croky-b/Boat_Engine_system_MAXI/Sound.ino

//
// =======================================================================================================
// SOUND
// =======================================================================================================
//




void triggerSound()
{
  if (Init)
  {
    
  Long_blast.Volume = LONG_VOL ;
  Short_blast.Volume = SHORT_VOL ;
  Bell.Volume = BELL_VOL ;
  Ancre.Volume = ANCOR_VOL ;
  Ambient.Volume = AMBIENT_VOL ;
  Seagull.Volume = SEAGULL_VOL ;
  Gun.Volume = GUN_VOL ;
  AAGun.Volume = AAGUN_VOL;
  Ring.Volume = ALARM2_VOL;
  Alarm.Volume = ALARM1_VOL;
  eleven1.Volume = ELEVEN1_VOL;
  eleven2.Volume = ELEVEN2_VOL;
  eleven3.Volume = ELEVEN3_VOL;
  eleven4.Volume = ELEVEN4_VOL;
  eleven5.Volume = ELEVEN5_VOL;
  eleven6.Volume = ELEVEN6_VOL;
  eleven7.Volume = ELEVEN7_VOL;
  eleven8.Volume = ELEVEN8_VOL;
  twelve1.Volume = TWELVE1_VOL;
  twelve2.Volume = TWELVE2_VOL;
  twelve3.Volume = TWELVE3_VOL;
  
    //
    // =======================================================================================================
    // STANDARD SOUND
    // =======================================================================================================
    //

    if (Seq6SoundPart1OnOff) {

#ifdef SEQ6_PART1_GUN

      if (Gun.Playing == false) {

        DacAudio.Play(&Gun, true);
      }
       if (Gun.TimeElapsed > 50 && Gun.TimeElapsed < 100 ) {
      cannonFlash = true;
    }

    else cannonFlash = false;
#endif

#ifdef SEQ6_PART1_AAGUN

      if (AAGun.Playing == false) {

        DacAudio.Play(&AAGun, true);
      }

       if (AAGun.TimeElapsed > 50 && AAGun.TimeElapsed < 80 ) {
      machinGunFlash = true;
    }

    else machinGunFlash = false;
#endif

#ifdef SEQ6_PART1_BELL

      if (Bell.Playing == false) {

        DacAudio.Play(&Bell, true);
      }
#endif

#ifdef SEQ6_PART1_SHORT

      if (Short_blast.Playing == false) {

        DacAudio.Play(&Short_blast, true);
      }
#endif

#ifdef SEQ6_PART1_LONG

      if (Long_blast.Playing == false) {

        DacAudio.Play(&Long_blast, true);
      }
#endif

#ifdef SEQ6_PART1_ALARM

      if (Alarm.Playing == false) {

        DacAudio.Play(&Alarm, true);
      }
#endif

#ifdef SEQ6_PART1_TWELVE1

      if (twelve1.Playing == false) {

        DacAudio.Play(&twelve1, true);
      }
#endif

#ifdef SEQ6_PART1_TWELVE2

      if (twelve2.Playing == false) {

        DacAudio.Play(&twelve2, true);
      }
#endif

#ifdef SEQ6_PART1_TWELVE3

      if (twelve3.Playing == false) {

        DacAudio.Play(&twelve3, true);
      }
#endif
    }


 if (Seq6SoundPart2OnOff) {

#ifdef SEQ6_PART2_GUN

      if (Gun.Playing == false) {

        DacAudio.Play(&Gun, true);
      }
       if (Gun.TimeElapsed > 50 && Gun.TimeElapsed < 100 ) {
      cannonFlash = true;
    }

    else cannonFlash = false;
#endif

#ifdef SEQ6_PART2_AAGUN

      if (AAGun.Playing == false) {

        DacAudio.Play(&AAGun, true);
      }

     if (AAGun.TimeElapsed > 50 && AAGun.TimeElapsed < 80 ) {
      machinGunFlash = true;
    }

    else machinGunFlash = false;
      
#endif

#ifdef SEQ6_PART2_BELL

      if (Bell.Playing == false) {

        DacAudio.Play(&Bell, true);
      }
#endif

#ifdef SEQ6_PART2_SHORT

      if (Short_blast.Playing == false) {

        DacAudio.Play(&Short_blast, true);
      }
#endif

#ifdef SEQ6_PART2_LONG

      if (Long_blast.Playing == false) {

        DacAudio.Play(&Long_blast, true);
      }
#endif

#ifdef SEQ6_PART2_ALARM

      if (Alarm.Playing == false) {

        DacAudio.Play(&Alarm, true);
      }
#endif

#ifdef SEQ6_PART2_TWELVE1

      if (twelve1.Playing == false) {

        DacAudio.Play(&twelve1, true);
      }
#endif

#ifdef SEQ6_PART2_TWELVE2

      if (twelve2.Playing == false) {

        DacAudio.Play(&twelve2, true);
      }
#endif

#ifdef SEQ6_PART2_TWELVE3

      if (twelve3.Playing == false) {

        DacAudio.Play(&twelve3, true);
      }
#endif
    }

 if (Seq6SoundPart3OnOff) {

#ifdef SEQ6_PART3_GUN

      if (Gun.Playing == false) {

        DacAudio.Play(&Gun, true);
      }

    if (Gun.TimeElapsed > 50 && Gun.TimeElapsed < 100 ) {
      cannonFlash = true;
    }

    else cannonFlash = false;
#endif

#ifdef SEQ6_PART3_AAGUN

      if (AAGun.Playing == false) {

        DacAudio.Play(&AAGun, true);
      }
 if (AAGun.TimeElapsed > 50 && AAGun.TimeElapsed < 80 ) {
      machinGunFlash = true;
    }

    else machinGunFlash = false;
#endif

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

      if (Long_blast.Playing == false) {

        DacAudio.Play(&Long_blast, true);
      }
#endif

#ifdef SEQ2_PART3_ALARM

      if (Alarm.Playing == false) {

        DacAudio.Play(&Alarm, true);
      }
#endif

#ifdef SEQ2_PART3_TWELVE1

      if (twelve1.Playing == false) {

        DacAudio.Play(&twelve1, true);
      }
#endif

#ifdef SEQ2_PART3_TWELVE2

      if (twelve2.Playing == false) {

        DacAudio.Play(&twelve2, true);
      }
#endif

#ifdef SEQ2_PART3_TWELVE3

      if (twelve3.Playing == false) {

        DacAudio.Play(&twelve3, true);
      }
#endif
    }

 if (Seq2SoundPart4OnOff) {

#ifdef SEQ2_PART4_GUN

      if (Gun.Playing == false) {

        DacAudio.Play(&Gun, true);
      }

       if (Gun.TimeElapsed > 50 && Gun.TimeElapsed < 100 ) {
      cannonFlash = true;
    }

    else cannonFlash = false;
#endif

#ifdef SEQ2_PART4_AAGUN

      if (AAGun.Playing == false) {

        DacAudio.Play(&AAGun, true);
      }

       if (AAGun.TimeElapsed > 50 && AAGun.TimeElapsed < 80 ) {
      machinGunFlash = true;
    }

    else machinGunFlash = false;
#endif

#ifdef SEQ2_PART4_BELL

      if (Bell.Playing == false) {

        DacAudio.Play(&Bell, true);
      }
#endif

#ifdef SEQ2_PART4_SHORT

      if (Short_blast.Playing == false) {

        DacAudio.Play(&Short_blast, true);
      }
#endif

#ifdef SEQ2_PART4_LONG

      if (Long_blast.Playing == false) {

        DacAudio.Play(&Long_blast, true);
      }
#endif

#ifdef SEQ2_PART4_ALARM

      if (Alarm.Playing == false) {

        DacAudio.Play(&Alarm, true);
      }
#endif

#ifdef SEQ2_PART4_TWELVE1

      if (twelve1.Playing == false) {

        DacAudio.Play(&twelve1, true);
      }
#endif

#ifdef SEQ2_PART4_TWELVE2

      if (twelve2.Playing == false) {

        DacAudio.Play(&twelve2, true);
      }
#endif

#ifdef SEQ2_PART4_TWELVE3

      if (twelve3.Playing == false) {

        DacAudio.Play(&twelve3, true);
      }
#endif
    }
    if (Seq60SoundPart1OnOff) {

#ifdef SEQ6B_PART1_GUN

      if (Gun.Playing == false) {

        DacAudio.Play(&Gun, true);
      }
       if (Gun.TimeElapsed > 50 && Gun.TimeElapsed < 100 ) {
      cannonFlash = true;
    }

    else cannonFlash = false;
#endif

#ifdef SEQ6B_PART1_AAGUN

      if (AAGun.Playing == false) {

        DacAudio.Play(&AAGun, true);
      }

       if (AAGun.TimeElapsed > 50 && AAGun.TimeElapsed < 80 ) {
      machinGunFlash = true;
    }

    else machinGunFlash = false;
#endif

#ifdef SEQ6B_PART1_BELL

      if (Bell.Playing == false) {

        DacAudio.Play(&Bell, true);
      }
#endif

#ifdef SEQ6B_PART1_SHORT

      if (Short_blast.Playing == false) {

        DacAudio.Play(&Short_blast, true);
      }
#endif

#ifdef SEQ6B_PART1_LONG

      if (Long_blast.Playing == false) {

        DacAudio.Play(&Long_blast, true);
      }
#endif

#ifdef SEQ6B_PART1_ALARM

      if (Alarm.Playing == false) {

        DacAudio.Play(&Alarm, true);
      }
#endif

#ifdef SEQ6B_PART1_TWELVE1

      if (twelve1.Playing == false) {

        DacAudio.Play(&twelve1, true);
      }
#endif

#ifdef SEQ6B_PART1_TWELVE2

      if (twelve2.Playing == false) {

        DacAudio.Play(&twelve2, true);
      }
#endif

#ifdef SEQ6B_PART1_TWELVE3

      if (twelve3.Playing == false) {

        DacAudio.Play(&twelve3, true);
      }
#endif
    }


 if (Seq60SoundPart2OnOff) {

#ifdef SEQ6B_PART2_GUN

      if (Gun.Playing == false) {

        DacAudio.Play(&Gun, true);
      }
       if (Gun.TimeElapsed > 50 && Gun.TimeElapsed < 100 ) {
      cannonFlash = true;
    }

    else cannonFlash = false;
#endif

#ifdef SEQ6B_PART2_AAGUN

      if (AAGun.Playing == false) {

        DacAudio.Play(&AAGun, true);
      }

     if (AAGun.TimeElapsed > 50 && AAGun.TimeElapsed < 80 ) {
      machinGunFlash = true;
    }

    else machinGunFlash = false;
      
#endif

#ifdef SEQ6B_PART2_BELL

      if (Bell.Playing == false) {

        DacAudio.Play(&Bell, true);
      }
#endif

#ifdef SEQ6B_PART2_SHORT

      if (Short_blast.Playing == false) {

        DacAudio.Play(&Short_blast, true);
      }
#endif

#ifdef SEQ6B_PART2_LONG

      if (Long_blast.Playing == false) {

        DacAudio.Play(&Long_blast, true);
      }
#endif

#ifdef SEQ6B_PART2_ALARM

      if (Alarm.Playing == false) {

        DacAudio.Play(&Alarm, true);
      }
#endif

#ifdef SEQ6B_PART2_TWELVE1

      if (twelve1.Playing == false) {

        DacAudio.Play(&twelve1, true);
      }
#endif

#ifdef SEQ6B_PART2_TWELVE2

      if (twelve2.Playing == false) {

        DacAudio.Play(&twelve2, true);
      }
#endif

#ifdef SEQ6B_PART2_TWELVE3

      if (twelve3.Playing == false) {

        DacAudio.Play(&twelve3, true);
      }
#endif
    }

 if (Seq60SoundPart3OnOff) {

#ifdef SEQ6B_PART3_GUN

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

      if (AAGun.Playing == false) {

        DacAudio.Play(&AAGun, true);
      }

       if (AAGun.TimeElapsed > 50 && AAGun.TimeElapsed < 80 ) {
      machinGunFlash = true;
    }

    else machinGunFlash = false;
#endif

#ifdef SEQ2B_PART3_BELL

      if (Bell.Playing == false) {

        DacAudio.Play(&Bell, true);
      }
#endif

#ifdef SEQ2B_PART3_SHORT

      if (Short_blast.Playing == false) {

        DacAudio.Play(&Short_blast, true);
      }
#endif

#ifdef SEQ2B_PART3_LONG

      if (Long_blast.Playing == false) {

        DacAudio.Play(&Long_blast, true);
      }
#endif

#ifdef SEQ2B_PART3_ALARM

      if (Alarm.Playing == false) {

        DacAudio.Play(&Alarm, true);
      }
#endif

#ifdef SEQ2B_PART3_TWELVE1

      if (twelve1.Playing == false) {

        DacAudio.Play(&twelve1, true);
      }
#endif

#ifdef SEQ2B_PART3_TWELVE2

      if (twelve2.Playing == false) {

        DacAudio.Play(&twelve2, true);
      }
#endif

#ifdef SEQ2B_PART3_TWELVE3

      if (twelve3.Playing == false) {

        DacAudio.Play(&twelve3, true);
      }
#endif
    }

 if (Seq20SoundPart4OnOff) {

#ifdef SEQ2B_PART4_GUN

      if (Gun.Playing == false) {

        DacAudio.Play(&Gun, true);
      }

       if (Gun.TimeElapsed > 50 && Gun.TimeElapsed < 100 ) {
      cannonFlash = true;
    }

    else cannonFlash = false;
#endif

#ifdef SEQ2B_PART4_AAGUN

      if (AAGun.Playing == false) {

        DacAudio.Play(&AAGun, true);
      }

       if (AAGun.TimeElapsed > 50 && AAGun.TimeElapsed < 80 ) {
      machinGunFlash = true;
    }

    else machinGunFlash = false;
#endif

#ifdef SEQ2B_PART4_BELL

      if (Bell.Playing == false) {

        DacAudio.Play(&Bell, true);
      }
#endif

#ifdef SEQ2B_PART4_SHORT

      if (Short_blast.Playing == false) {

        DacAudio.Play(&Short_blast, true);
      }
#endif

#ifdef SEQ2B_PART4_LONG

      if (Long_blast.Playing == false) {

        DacAudio.Play(&Long_blast, true);
      }
#endif

#ifdef SEQ2B_PART4_ALARM

      if (Alarm.Playing == false) {

        DacAudio.Play(&Alarm, true);
      }
#endif

#ifdef SEQ2B_PART4_TWELVE1

      if (twelve1.Playing == false) {

        DacAudio.Play(&twelve1, true);
      }
#endif

#ifdef SEQ2B_PART4_TWELVE2

      if (twelve2.Playing == false) {

        DacAudio.Play(&twelve2, true);
      }
#endif

#ifdef SEQ2B_PART4_TWELVE3

      if (twelve3.Playing == false) {

        DacAudio.Play(&twelve3, true);
      }
#endif
    }
#ifdef ANCHORSOUND
    Ancre.Volume = 50;

    if (Mouillage && !AncreBas ) {
      AncreStop = false;

      if ( Ancre.Playing == true && Ancre.TimeElapsed > 10000) {
        AncreBas = true;
      }
      if (Ancre.Playing == false) {
        DacAudio.Play(&Ancre, true);
      }
    }


    else if (!Mouillage && AncreBas ) {
      AncreStop = false;

      if ( Ancre.Playing == true && Ancre.TimeElapsed > 10000) {
        AncreBas = false;
      }
      if (Ancre.Playing == false) {
        DacAudio.Play(&Ancre, true);
      }
    }


    if (Ancre.Playing == false) {
      AncreStop = true;
    }


    if (!AncreBas && Ancre.Playing == true && Ancre.TimeElapsed > 8000 && Ancre.TimeElapsed < 10500) {
      if (AnchorSpeedDown > 1500){
      AnchorSpeedDown -= 2;
      if (AnchorSpeedDown < 1500 ) {
        AnchorSpeedDown = 1500;
      }
      }
      if (AnchorSpeedDown < 1500){
      AnchorSpeedDown += 2;
      if (AnchorSpeedDown > 1500 ) {
        AnchorSpeedDown = 1500;
      }
      }
    }

    if (AncreBas && Ancre.Playing == true && Ancre.TimeElapsed > 8000 && Ancre.TimeElapsed < 10500) {

      if (AnchorSpeedUp <1500){
      AnchorSpeedUp += 2;
      if ( AnchorSpeedUp > 1500 ) {
        AnchorSpeedUp = 1500;
      }
      }

      if (AnchorSpeedUp >1500){
      AnchorSpeedUp -= 2;
      if ( AnchorSpeedUp < 1500 ) {
        AnchorSpeedUp = 1500;
      }
      }

      
    }

#endif


#ifdef ACTION3_ENABLE
    if (Fog)
    {

      if (engineOn && !Fishing && !Mouillage) {

        //Son Long toutes les 2min
#if not defined PILOTBOAT
        if (millis() - FogSoundMillis > 120000) {
          FogSoundMillis = millis();
          Sequence6.RemoveAllPlayItems();
          sequence6();
          DacAudio.Play(&Sequence6, true);
        }

#else
        //4 son courts
        if (millis() - FogSoundMillis > 120000) {
          FogSoundMillis = millis();
          Sequence15.RemoveAllPlayItems();
          sequence15();
          DacAudio.Play(&Sequence15, true);

        }
#endif

      }

      // Sons Long et 2 courts toutes les 2min
      if (engineOn && Fishing) {
        // Bateau remorqué 1 Son long 3 courts
#if defined OTHERBOAT
        if (millis() - FogSoundMillis > 120000) {
          FogSoundMillis = millis();
          Sequence16.RemoveAllPlayItems();
          sequence16();
          DacAudio.Play(&Sequence16, true);
        }
        // 4 sons courts toutes les 2min
#elif defined PILOTBOAT //defined
        if (millis() - FogSoundMillis > 120000) {
          FogSoundMillis = millis();
          Sequence15.RemoveAllPlayItems();
          sequence15();
          DacAudio.Play(&Sequence15, true);
        }
        // Sons Long et 2 courts toutes les 2min
#else
        if (millis() - FogSoundMillis > 120000) {
          FogSoundMillis = millis();
          Sequence8.RemoveAllPlayItems();
          sequence8();
          DacAudio.Play(&Sequence8, true);
        }
#endif
      }


      //2 sons Long toutes les 2min
      if (!engineOn && !Fishing && !Mouillage) {
        if (millis() - FogSoundMillis > 120000) {
          FogSoundMillis = millis();
          Sequence7.RemoveAllPlayItems();
          sequence7();
          DacAudio.Play(&Sequence7, true);
        }
      }
      //cloche tout le minute
//#ifdef ACTION2_ENABLE
      if (!engineOn && Mouillage) {
        if (millis() - BellMillis > 60000) {

          BellMillis = millis();
//#endif
#ifdef INTER
          Sequence10.RemoveAllPlayItems();
          sequence10();
          DacAudio.Play(&Sequence10, true);
#endif

#ifdef SHORT

          Sequence14.RemoveAllPlayItems();
          sequence14();
          DacAudio.Play(&Sequence14, true);
#endif

        }
      }

    }
#endif

#ifdef ACTION4_ENABLE

    if ( engineOn) {

      if (Maneuvre ) {

        /// marche arriere 3 Sons bref
        if (CH3.momentaryPos() == 1) {

          if (Sequence5.Playing == false) {
            Sequence5.RemoveAllPlayItems();
            sequence5();
            DacAudio.Play(&Sequence5, true);
          }
        }

        /// Vire a gauche deux sons court
        if (CH1.momentaryPos() == 1)
        {

          if (Sequence3.Playing == false) {
            Sequence3.RemoveAllPlayItems();
            sequence3();
            DacAudio.Play(&Sequence3, true);
          }


        }
        /// Vire a droite 1 son court
        else if (CH1.momentaryPos() == 3)
        {
          if (Sequence4.Playing == false) {

            Sequence4.RemoveAllPlayItems();
            sequence4();
            DacAudio.Play(&Sequence4, true);
          }

        }

        else  {
        }

      }
    }

#endif

#ifdef ACTION5_ENABLE

    if ( engineOn) {


      if (Avertissement ) {

        if ((Short_blast.TimeElapsed > 5 && Short_blast.TimeElapsed < 1200 ) || (Long_blast.TimeElapsed > 5 && Long_blast.TimeElapsed < 3600 ))
        {
          Manoeuvre_Led = true;
        }

        else {
          Manoeuvre_Led = false;
        }

        /// Depasse par la gauche 2 Long 2 court
        if (CH4.momentaryPos() == 1)
        {
          if (Sequence1.Playing == false) {
            Sequence1.RemoveAllPlayItems();
            sequence1();
            DacAudio.Play(&Sequence1, true);
          }

        }
        /// Depasse par la droite  deux long 1 court
        else if (CH4.momentaryPos() == 3)
        {
          if (Sequence2.Playing == false) {
            Sequence2.RemoveAllPlayItems();
            sequence2();
            DacAudio.Play(&Sequence2, true);
          }

        }

        else  {

        }

        /// Acceptation Long court long court
        if (CH2.momentaryPos() == 3)
        {
          if (Sequence13.Playing == false) {
            Sequence13.RemoveAllPlayItems();
            sequence13();
            DacAudio.Play(&Sequence13, true);
          }

        }


      }
    }

#endif



    //
    // =======================================================================================================
    // SPECIAL SOUND
    // =======================================================================================================
    //

#ifdef ACTION8_ENABLE
#if defined RINGALARM

    if (Ring_Sound) {

      if (Ring.Playing == false) {

        DacAudio.Play(&Ring, true);
      }
    }

    if (Alarm_Sound) {

      if (Alarm.Playing == false) {

        DacAudio.Play(&Alarm, true);
      }

      if (Ring.Playing == false) {
        DacAudio.Play(&Ring, true);
      }
    }

#else
    if (Alarm_Sound) {

      if (Alarm.Playing == false) {

        DacAudio.Play(&Alarm, true);
      }

    }

#endif

#endif

#ifdef ACTION6_ENABLE
    if (MachineGunSound ) {

      if (Sequence12.Playing == false) {
        Sequence12.RemoveAllPlayItems();
        sequence12();
        DacAudio.Play(&Sequence12, true);
      }
    }


    if (AAGun.TimeElapsed > 50 && AAGun.TimeElapsed < 80 ) {
      machinGunFlash = true;
    }

    else machinGunFlash = false;

#endif

#ifdef ACTION7_ENABLE

    if (GunSound2 ) {

      if (Sequence11.Playing == false) {
        Sequence11.RemoveAllPlayItems();

        sequence11();

        DacAudio.Play(&Sequence11, true);
      }

    }

    if (Gun.TimeElapsed > 50 && Gun.TimeElapsed < 100 ) {
      cannonFlash = true;
    }

    else cannonFlash = false;

#endif




 #ifdef ACTION11A_ENABLE

 #ifdef ACTION11A_HIGH_REPEAT_FOREVER

    #ifdef ACTION11A_UP_MULTISWITCH
      if (Act11A_UP) {
    #else      
      if (Action11A.Pos()== 3) {
    #endif
 #else 
      #ifdef ACTION11A_UP_MULTISWITCH
      if (Act11A_UP) {
      #else        
      if (Action11A.momentaryPos()== 3) {
      #endif 
 #endif   
 
      
 
    #ifdef ACTION11A_HIGH_PERSO_1
      #ifdef ACTION11A_HIGH_REPEAT_FOREVER
    
     #else
     eleven1.Repeat= ACTION11A_HIGH_REPEAT;
     #endif
       if (eleven1.Playing == false) {
        DacAudio.Play(&eleven1, true);
      }
     #endif

       #ifdef ACTION11A_HIGH_PERSO_2

     #ifdef ACTION11A_HIGH_REPEAT_FOREVER
    
     #else
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
      }
    
    #endif

    #ifdef ACTION11D_LOW_PERSO_7
       #ifdef ACTION11D_LOW_REPEAT_FOREVER
    
     #else
     eleven7.Repeat= ACTION11D_LOW_REPEAT;
     #endif
       if (eleven7.Playing == false) {
        DacAudio.Play(&eleven7, true);
      }
    
    #endif

    #ifdef ACTION11D_LOW_PERSO_8
       #ifdef ACTION11D_LOW_REPEAT_FOREVER
    
     #else
     eleven8.Repeat= ACTION11D_LOW_REPEAT;
     #endif
       if (eleven8.Playing == false) {
        DacAudio.Play(&eleven8, true);
      }
  
    #endif

      #ifdef ACTION11D_LOW_SEAGULL
    #ifdef ACTION11D_LOW_REPEAT_FOREVER
    
     #else
     Seagull.Repeat= ACTION11D_LOW_REPEAT;
     #endif
       if (Seagull.Playing == false) {
        DacAudio.Play(&Seagull, true);
      }
    
    #endif

    #ifdef ACTION11D_LOW_AMBIENT
    #ifdef ACTION11D_LOW_REPEAT_FOREVER
    
     #else
     Ambient.Repeat= ACTION11D_LOW_REPEAT;
     #endif
       if (Ambient.Playing == false) {
        DacAudio.Play(&Ambient, true);
      }
  
    #endif
   
  }
 #endif

#ifdef ACTION12_ENABLE

    if (MachineGunSound ) {

      if (Sequence12.Playing == false) {
        Sequence12.RemoveAllPlayItems();
        sequence12();
        DacAudio.Play(&Sequence12, true);
      }
    }


    if (AAGun.TimeElapsed > 50 && AAGun.TimeElapsed < 80 ) {
      machinGunFlash = true;
    }

    else machinGunFlash = false;

    if (GunSound ) {

      if (Sequence11.Playing == false) {
        Sequence11.RemoveAllPlayItems();

        sequence11();

        DacAudio.Play(&Sequence11, true);
      }

    }

    if (Gun.TimeElapsed > 50 && Gun.TimeElapsed < 100 ) {
      cannonFlash = true;
    }

    else cannonFlash = false;


    if (Act12Sound1 ) {

      if (twelve1.Playing == false) {
        DacAudio.Play(&twelve1, true);
      }

    }

    if (Act12Sound2 ) {

      if (twelve2.Playing == false) {
        DacAudio.Play(&twelve2, true);
      }

    }

    if (Act12Sound3 ) {

      if (twelve3.Playing == false) {
        DacAudio.Play(&twelve3, true);
      }

    }


#endif


  } //fin init
}// fin triggersound




// Avertissement demande par babord
void sequence1() {



  Sequence1.AddPlayItem(&Long_blast);
  Sequence1.AddPlayItem(&Long_blast);
  Sequence1.AddPlayItem(&Short_blast);
  Sequence1.AddPlayItem(&Short_blast);

}

// Avertissement demande par tribord
void sequence2() {


  Sequence2.AddPlayItem(&Long_blast);
  Sequence2.AddPlayItem(&Long_blast);
  Sequence2.AddPlayItem(&Short_blast);

}
//manoeuvre babord
void sequence3() {

  Sequence3.AddPlayItem(&Short_blast);
  Sequence3.AddPlayItem(&Short_blast);

}
//manoeuvre tribord
void sequence4() {

  Sequence4.AddPlayItem(&Short_blast);

}

//manoeuvre battre en arriere
void sequence5() {

  Sequence5.AddPlayItem(&Short_blast);
  Sequence5.AddPlayItem(&Short_blast);
  Sequence5.AddPlayItem(&Short_blast);
}

// avec erre
void sequence6() {

  Sequence6.AddPlayItem(&Long_blast);

}
//sans erre
void sequence7() {

  Sequence7.AddPlayItem(&Long_blast);
  Sequence7.AddPlayItem(&Long_blast);
}
//navire privilegie
void sequence8() {

  Sequence8.AddPlayItem(&Long_blast);
  Sequence8.AddPlayItem(&Short_blast);
  Sequence8.AddPlayItem(&Short_blast);
}
//mouillage +20m
void sequence10() {

  Sequence10.AddPlayItem(&Bell);

}
//canon
void sequence11() {

  Sequence11.AddPlayItem(&Gun);

}
//mitraillette
void sequence12() {

  Sequence12.AddPlayItem(&AAGun);
  Sequence12.AddPlayItem(&AAGun);
  Sequence12.AddPlayItem(&AAGun);
  Sequence12.AddPlayItem(&AAGun);
  Sequence12.AddPlayItem(&AAGun);
  Sequence12.AddPlayItem(&AAGun);
  Sequence12.AddPlayItem(&AAGun);
  Sequence12.AddPlayItem(&AAGun);
  Sequence12.AddPlayItem(&AAGun);
  Sequence12.AddPlayItem(&AAGun);
  Sequence12.AddPlayItem(&AAGun);
  Sequence12.AddPlayItem(&AAGun);
  Sequence12.AddPlayItem(&AAGun);
  Sequence12.AddPlayItem(&AAGun);
  Sequence12.AddPlayItem(&AAGun);
  Sequence12.AddPlayItem(&AAGun);
  Sequence12.AddPlayItem(&AAGun);
  Sequence12.AddPlayItem(&AAGun);


}

// Avertissement acceptation
void sequence13() {


  Sequence13.AddPlayItem(&Long_blast);
  Sequence13.AddPlayItem(&Short_blast);
  Sequence13.AddPlayItem(&Long_blast);
  Sequence13.AddPlayItem(&Short_blast);

}
// mouillage -20m
void sequence14() {

  Sequence14.AddPlayItem(&Short_blast);
  Sequence14.AddPlayItem(&Long_blast);
  Sequence14.AddPlayItem(&Short_blast);

}
// pilot boat
void sequence15() {

  Sequence15.AddPlayItem(&Short_blast);
  Sequence15.AddPlayItem(&Short_blast);
  Sequence15.AddPlayItem(&Short_blast);
  Sequence15.AddPlayItem(&Short_blast);

}

// Remorqué
void sequence16() {

  Sequence16.AddPlayItem(&Long_blast);
  Sequence16.AddPlayItem(&Short_blast);
  Sequence16.AddPlayItem(&Short_blast);
  Sequence16.AddPlayItem(&Short_blast);

}
