croky-b/Boat_Engine_system_MAXI/Led.ino

// =======================================================================================================
// LED
// =======================================================================================================

void led() {

      if(Seq1LedPart1OnOff){
                #ifdef SEQ1_LED_HALOGEN_PART1_1
                Led1.halogenOn(0,1,1);
                #endif
                #ifdef SEQ1_LED_HALOGEN_PART1_2
                Led2.halogenOn(1,1,1);
                #endif
                #ifdef SEQ1_LED_HALOGEN_PART1_3
                Led3.halogenOn(2,1,1);
                #endif
                #ifdef SEQ1_LED_HALOGEN_PART1_4
                Led4.halogenOn(3,1,1);
                #endif
                #ifdef SEQ1_LED_HALOGEN_PART1_5
                Led5.halogenOn(4,1,1);
                #endif
                #ifdef SEQ1_LED_HALOGEN_PART1_6
                Led6.halogenOn(5,1,1);
                #endif
                #ifdef SEQ1_LED_HALOGEN_PART1_7
                Led7.halogenOn(6,1,1);
                #endif
                #ifdef SEQ1_LED_HALOGEN_PART1_8
                Led8.halogenOn(7,1,1);
                #endif
                #ifdef SEQ1_LED_HALOGEN_PART1_9
                Led9.halogenOn(8,1,1);
                #endif
                #ifdef SEQ1_LED_HALOGEN_PART1_10
                Led10.halogenOn(9,1,1);
                #endif
                #ifdef SEQ1_LED_HALOGEN_PART1_11
                Led11.halogenOn(12,1,1);
                #endif
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
                Led12.Off(13);
                #endif
                #ifdef SEQ2_FLASH_SPEC_PART1_13
                Led13.Off(14);
                #endif
                #ifdef SEQ2_FLASH_SPEC_PART1_14
                Led14.Off(14);
                #endif
        ////////////////////////
  }
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
